jgOhYeah/FarmBaseStation/BaseStationCode/src/src/rpc.h

/**
 * @file rpc.h
 * @brief Handles RPC calls.
 * 
 * @author Jotham Gates
 * @version 0.1
 * @date 2023-08-12
 */

#pragma once
#include "../defines.h"
#include "topics.h"
#include "alarm.h"
#include "devices.h"
#include "fields.h"
#include "networking.h"

/**
 * @brief Function that is called when an mqtt message is received.
 *
 */
void mqttReceived(char *topic, byte *message, unsigned int length);

/**
 * @brief Handles an RPC message addressed to this device (not one of the remote devices).
 * 
 * @param id id number as a char array to reply with.
 * @param message the incoming message.
 * @param length the length of the incoming message.
 */
void rpcMe(char *id, uint8_t *message, uint16_t length);

/**
 * @brief Replies to an RPC message for this device.
 * 
 * @param id char array of the request ID.
 * @param reply the payload to return.
 */
void replyMeRpc(char *id, char *reply);

/**
 * @brief Handles an RPC message addressed to remote devices.
 * 
 * @param id id number as a char array to reply with.
 * @param message the incoming message.
 * @param length the length of the incoming message.
 */
void rpcGateway(uint8_t *message, uint16_t length);

/**
 * @brief Checks if one string starts with another (quicker than strstr?)
 *
 * @param input the string to be checked.
 * @param compare what to look for.
 * @return Whether input starts with compare.
 */
bool startsWith(char *input, const char *compare);

/**
 * @brief Sets the state of an attribute.
 * 
 */
void setAttributeState(const char* const attribute, bool state);

/**
 * @brief Informs thingsboard what software version is running.
 * This does not use a queue as this could be sent upon reconnecting when the queue is full and before it has had a chance to recover, thus blocking forever if a queue is used.
 * 
 */
void setVersionAttribute();

/**
 * @brief Converts a reset reason returned by `esp_reset_reason()` into a string.
 * 
 * This is copied from the ResetReason2 esp32 example.
 * 
 * @param reason the reset reason returned by `esp_reset_reason()`.
 * @return const char* A string representing the reason.
 */
const char *resetReasonName(esp_reset_reason_t reason);

#ifdef PIN_IR
/**
 * @brief Sends an infrared command to the air conditioner.
 * 
 * @param obj JSON containing parameters to send.
 * @return true on success.
 * @return false on parameter issues.
 */
bool sendAirConditioner(JsonObject obj, JsonDocument &reply);

/**
 * @brief Saves the current air conditioner settings to a JSON object.
 * 
 * @param obj object to save to.
 */
void airConditionerReplySettings(JsonDocument &obj);

/**
 * @brief Sets the air conditioner attributes. This is useful for some of the buttons.
 * 
 * @param payload the serialised JsonDocument set by airConditionerReplySettings().
 */
void setAirConditionerAttribute(const char* payload);

/**
 * @brief Sets the air conditioner attributes without using a queue. This is good for syncing the default settings with Thingsboard on first boot.
 * 
 */
void setAirConditionerAttributeInitial();
#endif
