jgOhYeah/FarmBaseStation/BaseStationCode/src/src/networking.h

/**
 * @file networking.h
 * @brief Header file for networking.cpp
 *
 * @author Jotham Gates
 * @version 0.1
 * @date 2023-08-12
 */
#pragma once
#include "../defines.h"
#include "devices.h"
#include "lora.h"

struct MqttMsg
{
    const char* topic;
    char payload[MAX_JSON_TEXT_LENGTH];
};

enum NetworkState {NETWORK_NONE, NETWORK_WIFI_CONNECTING, NETWORK_MQTT_CONNECTING, NETWORK_CONNECTED};

#ifdef USE_ETHERNET
void onEthernetEvent(arduino_event_id_t event);
#else
void wifiConnect();
#endif
void mqttReceived(char *topic, byte *message, unsigned int length);
void mqttConnect();
void mqttSetup();
void networkingTask(void *pvParameters);
